Elecrow-RD/All-in-one-Starter-Kit-for-ESP32-P4-with-Common-Board-design/example/V1.1/Arduino_code/Lesson09_Display/esp_panel_drivers_conf.h

/*
 * SPDX-FileCopyrightText: 2023-2025 Espressif Systems (Shanghai) CO LTD
 *
 * SPDX-License-Identifier: Apache-2.0
 */
/**
 * @file  esp_panel_drivers_conf.h
 * @brief Configuration file for ESP Panel Drivers
 *
 * This file contains all the configurations needed for ESP Panel Drivers.
 * Users can modify these configurations according to their requirements.
 */

#pragma once

// *INDENT-OFF*

////////////////////////////////////////////////////////////////////////////////////////////////////////////////////////
////////////////////////////////////////////////// Bus Configurations //////////////////////////////////////////////////
////////////////////////////////////////////////////////////////////////////////////////////////////////////////////////
/**
 * @brief Bus driver availability
 *
 * Enable or disable bus drivers used in the factory class. Disable to reduce code size.
 * Set to `1` to enable, `0` to disable.
 */
#define ESP_PANEL_DRIVERS_BUS_USE_ALL                   (1)
#if !ESP_PANEL_DRIVERS_BUS_USE_ALL
    #define ESP_PANEL_DRIVERS_BUS_USE_SPI               (0)
    #define ESP_PANEL_DRIVERS_BUS_USE_QSPI              (0)
    #define ESP_PANEL_DRIVERS_BUS_USE_RGB               (0)
    #define ESP_PANEL_DRIVERS_BUS_USE_I2C               (0)
    #define ESP_PANEL_DRIVERS_BUS_USE_MIPI_DSI          (1)
#endif // ESP_PANEL_DRIVERS_BUS_USE_ALL

/**
 * @brief Controls compilation of unused bus drivers
 *
 * Enable or disable compilation of unused bus drivers.
 * When set to `0`, code for unused bus drivers will be excluded to speed up compilation. At this time,
 * users should ensure that the bus driver is not used.
 *
 * Example with SPI:
 * (CONF1 = ESP_PANEL_DRIVERS_BUS_USE_SPI, CONF2 = ESP_PANEL_DRIVERS_BUS_COMPILE_UNUSED_DRIVERS)
 *
 * | CONF1 | CONF2 | Driver Available ( = CONF1 ^ CONF2) | Factory Support ( = CONF1) |
 * |-------|-------|-------------------------------------|----------------------------|
 * |   0   |   0   |                 No                  |              No            |
 * |   1   |   0   |                 Yes                 |              Yes           |
 * |   0   |   1   |                 Yes                 |              No            |
 * |   1   |   1   |                 Yes                 |              Yes           |
 */
#define ESP_PANEL_DRIVERS_BUS_COMPILE_UNUSED_DRIVERS    (1)

////////////////////////////////////////////////////////////////////////////////////////////////////////////////////////
///////////////////////////////////////////////// LCD Configurations ///////////////////////////////////////////////////
////////////////////////////////////////////////////////////////////////////////////////////////////////////////////////
/**
 * @brief LCD driver availability
 *
 * Enable or disable LCD drivers used in the factory class. Disable to reduce code size.
 * Set to `1` to enable, `0` to disable.
 */
#define ESP_PANEL_DRIVERS_LCD_USE_ALL                   (0)
#if !ESP_PANEL_DRIVERS_LCD_USE_ALL
    #define ESP_PANEL_DRIVERS_LCD_USE_AXS15231B         (0)
    #define ESP_PANEL_DRIVERS_LCD_USE_EK9716B           (0)
    #define ESP_PANEL_DRIVERS_LCD_USE_EK79007           (1)
    #define ESP_PANEL_DRIVERS_LCD_USE_GC9A01            (0)
    #define ESP_PANEL_DRIVERS_LCD_USE_GC9B71            (0)
    #define ESP_PANEL_DRIVERS_LCD_USE_GC9503            (0)
    #define ESP_PANEL_DRIVERS_LCD_USE_HX8399            (0)
    #define ESP_PANEL_DRIVERS_LCD_USE_ILI9341           (0)
    #define ESP_PANEL_DRIVERS_LCD_USE_ILI9881C          (0)
    #define ESP_PANEL_DRIVERS_LCD_USE_JD9165            (0)
    #define ESP_PANEL_DRIVERS_LCD_USE_JD9365            (0)
    #define ESP_PANEL_DRIVERS_LCD_USE_NV3022B           (0)
    #define ESP_PANEL_DRIVERS_LCD_USE_SH8601            (0)
    #define ESP_PANEL_DRIVERS_LCD_USE_SPD2010           (0)
    #define ESP_PANEL_DRIVERS_LCD_USE_ST7262            (0)
    #define ESP_PANEL_DRIVERS_LCD_USE_ST7701            (0)
    #define ESP_PANEL_DRIVERS_LCD_USE_ST7703            (0)
    #define ESP_PANEL_DRIVERS_LCD_USE_ST7789            (0)
    #define ESP_PANEL_DRIVERS_LCD_USE_ST7796            (0)
    #define ESP_PANEL_DRIVERS_LCD_USE_ST77903           (0)
    #define ESP_PANEL_DRIVERS_LCD_USE_ST77916           (0)
    #define ESP_PANEL_DRIVERS_LCD_USE_ST77922           (0)
#endif // ESP_PANEL_DRIVERS_LCD_USE_ALL

/**
 * @brief Controls compilation of unused LCD drivers
 *
 * Enable or disable compilation of unused LCD drivers.
 * When set to `0`, code for unused LCD drivers will be excluded to speed up compilation. At this time,
 * users should ensure that the LCD driver is not used.
 *
 * Example with ILI9341:
 * (CONF1 = ESP_PANEL_DRIVERS_LCD_USE_ILI9341, CONF2 = ESP_PANEL_DRIVERS_LCD_COMPILE_UNUSED_DRIVERS)
 *
 * | CONF1 | CONF2 | Driver Available ( = CONF1 ^ CONF2) | Factory Support ( = CONF1) |
 * |-------|-------|-------------------------------------|----------------------------|
 * |   0   |   0   |                 No                  |              No            |
 * |   1   |   0   |                 Yes                 |              Yes           |
 * |   0   |   1   |                 Yes                 |              No            |
 * |   1   |   1   |                 Yes                 |              Yes           |
 */
#define ESP_PANEL_DRIVERS_LCD_COMPILE_UNUSED_DRIVERS    (1)

////////////////////////////////////////////////////////////////////////////////////////////////////////////////////////
///////////////////////////////////////////////// Touch Configurations /////////////////////////////////////////////////
////////////////////////////////////////////////////////////////////////////////////////////////////////////////////////
/**
 * @brief Touch panel configuration parameters
 */
#define ESP_PANEL_DRIVERS_TOUCH_MAX_POINTS              (10)    // Maximum number of touch points supported
#define ESP_PANEL_DRIVERS_TOUCH_MAX_BUTTONS             (5)     // Maximum number of touch buttons supported

/**
 * @brief Touch driver availability
 *
 * Enable or disable touch drivers used in the factory class. Disable to reduce code size.
 * Set to `1` to enable, `0` to disable.
 */
#define ESP_PANEL_DRIVERS_TOUCH_USE_ALL                 (0)
#if !ESP_PANEL_DRIVERS_TOUCH_USE_ALL
    #define ESP_PANEL_DRIVERS_TOUCH_USE_AXS15231B       (0)
    #define ESP_PANEL_DRIVERS_TOUCH_USE_CHSC6540        (0)
    #define ESP_PANEL_DRIVERS_TOUCH_USE_CST816S         (0)
    #define ESP_PANEL_DRIVERS_TOUCH_USE_CST820          (0)
    #define ESP_PANEL_DRIVERS_TOUCH_USE_FT5x06          (0)
    #define ESP_PANEL_DRIVERS_TOUCH_USE_GT911           (1)
    #define ESP_PANEL_DRIVERS_TOUCH_USE_GT1151          (0)
    #define ESP_PANEL_DRIVERS_TOUCH_USE_SPD2010         (0)
    #define ESP_PANEL_DRIVERS_TOUCH_USE_ST1633          (0)
    #define ESP_PANEL_DRIVERS_TOUCH_USE_ST7123          (0)
    #define ESP_PANEL_DRIVERS_TOUCH_USE_STMPE610        (0)
    #define ESP_PANEL_DRIVERS_TOUCH_USE_TT21100         (0)
    #define ESP_PANEL_DRIVERS_TOUCH_USE_XPT2046         (0)
#endif // ESP_PANEL_DRIVERS_TOUCH_USE_ALL

/**
 * @brief Controls compilation of unused touch drivers
 *
 * Enable or disable compilation of unused touch drivers.
 * When set to `0`, code for unused touch drivers will be excluded to speed up compilation. At this time,
 * users should ensure that the touch driver is not used.
 *
 * Example with GT911:
 * (CONF1 = ESP_PANEL_DRIVERS_TOUCH_USE_GT911, CONF2 = ESP_PANEL_DRIVERS_TOUCH_COMPILE_UNUSED_DRIVERS)
 *
 * | CONF1 | CONF2 | Driver Available ( = CONF1 ^ CONF2) | Factory Support ( = CONF1) |
 * |-------|-------|-------------------------------------|----------------------------|
 * |   0   |   0   |                 No                  |              No            |
 * |   1   |   0   |                 Yes                 |              Yes           |
 * |   0   |   1   |                 Yes                 |              No            |
 * |   1   |   1   |                 Yes                 |              Yes           |
 */
#define ESP_PANEL_DRIVERS_TOUCH_COMPILE_UNUSED_DRIVERS          (1)

#if ESP_PANEL_DRIVERS_TOUCH_USE_XPT2046 || ESP_PANEL_DRIVERS_TOUCH_COMPILE_UNUSED_DRIVERS
/**
 * @brief XPT2046 touch panel specific configurations
 */

#define ESP_PANEL_DRIVERS_TOUCH_XPT2046_Z_THRESHOLD             (400)  // Minimum pressure threshold for touch detection

/**
 * @brief Enable interrupt (PENIRQ) output mode
 *
 * When enabled, XPT2046 outputs low on PENIRQ when touch is detected (Full Power Mode).
 * Consumes more power but provides interrupt capability.
 */
#define ESP_PANEL_DRIVERS_TOUCH_XPT2046_INTERRUPT_MODE          (0)

/**
 * @brief Keep internal voltage reference enabled
 *
 * When enabled, internal Vref remains on between conversions. Slightly higher power consumption,
 * but requires fewer transactions for battery voltage, aux voltage and temperature readings.
 */
#define ESP_PANEL_DRIVERS_TOUCH_XPT2046_VREF_ON_MODE            (0)

/**
 * @brief Enable automatic coordinate conversion
 *
 * When enabled, raw ADC values (0-4096) are converted to screen coordinates.
 * When disabled, `process_coordinates` must be called manually to convert values.
 */
#define ESP_PANEL_DRIVERS_TOUCH_XPT2046_CONVERT_ADC_TO_COORDS   (1)

/**
 * @brief Enable data structure locking
 *
 * When enabled, driver locks touch position data structures during reads.
 * Warning: May cause unexpected crashes.
 */
#define ESP_PANEL_DRIVERS_TOUCH_XPT2046_ENABLE_LOCKING          (0)
#endif // ESP_PANEL_DRIVERS_TOUCH_USE_XPT2046 || ESP_PANEL_DRIVERS_TOUCH_COMPILE_UNUSED_DRIVERS

////////////////////////////////////////////////////////////////////////////////////////////////////////////////////////
////////////////////////////////////////////// IO Expander Configurations //////////////////////////////////////////////
////////////////////////////////////////////////////////////////////////////////////////////////////////////////////////
/**
 * @brief IO Expander driver availability
 *
 * Enable or disable IO Expander drivers used in the factory class. Disable to reduce code size.
 * Set to `1` to enable, `0` to disable.
 */
#define ESP_PANEL_DRIVERS_EXPANDER_USE_ALL                      (0)
#if !ESP_PANEL_DRIVERS_EXPANDER_USE_ALL
    #define ESP_PANEL_DRIVERS_EXPANDER_USE_CH422G               (0)
    #define ESP_PANEL_DRIVERS_EXPANDER_USE_HT8574               (0)
    #define ESP_PANEL_DRIVERS_EXPANDER_USE_TCA95XX_8BIT         (0)
    #define ESP_PANEL_DRIVERS_EXPANDER_USE_TCA95XX_16BIT        (0)
#endif // ESP_PANEL_DRIVERS_EXPANDER_USE_ALL

////////////////////////////////////////////////////////////////////////////////////////////////////////////////////////
/////////////////////////////////////////////// Backlight Configurations ///////////////////////////////////////////////
////////////////////////////////////////////////////////////////////////////////////////////////////////////////////////
/**
 * @brief Backlight driver availability
 *
 * Enable or disable backlight drivers used in the factory class. Disable to reduce code size.
 * Set to `1` to enable, `0` to disable.
 */
#define ESP_PANEL_DRIVERS_BACKLIGHT_USE_ALL                     (1)
#if !ESP_PANEL_DRIVERS_BACKLIGHT_USE_ALL
    #define ESP_PANEL_DRIVERS_BACKLIGHT_USE_SWITCH_GPIO         (0)
    #define ESP_PANEL_DRIVERS_BACKLIGHT_USE_SWITCH_EXPANDER     (0)
    #define ESP_PANEL_DRIVERS_BACKLIGHT_USE_PWM_LEDC            (0)
    #define ESP_PANEL_DRIVERS_BACKLIGHT_USE_CUSTOM              (0)
#endif // ESP_PANEL_DRIVERS_BACKLIGHT_USE_ALL

/**
 * @brief Controls compilation of unused backlight drivers
 *
 * Enable or disable compilation of unused backlight drivers.
 * When set to `0`, code for unused backlight drivers will be excluded to speed up compilation. At this time,
 * users should ensure that the backlight driver is not used.
 *
 * Example with PWM_LEDC:
 * (CONF1 = ESP_PANEL_DRIVERS_BACKLIGHT_USE_PWM_LEDC, CONF2 = ESP_PANEL_DRIVERS_BACKLIGHT_COMPILE_UNUSED_DRIVERS)
 *
 * | CONF1 | CONF2 | Driver Available ( = CONF1 ^ CONF2) | Factory Support ( = CONF1) |
 * |-------|-------|-------------------------------------|----------------------------|
 * |   0   |   0   |                 No                  |              No            |
 * |   1   |   0   |                 Yes                 |              Yes           |
 * |   0   |   1   |                 Yes                 |              No            |
 * |   1   |   1   |                 Yes                 |              Yes           |
 */
#define ESP_PANEL_DRIVERS_BACKLIGHT_COMPILE_UNUSED_DRIVERS     (1)

////////////////////////////////////////////////////////////////////////////////////////////////////////////////////////
/////////////////////////////////////////////// File Version ///////////////////////////////////////////////////////////
////////////////////////////////////////////////////////////////////////////////////////////////////////////////////////
/**
 * Do not change the following versions. These version numbers are used to check compatibility between this
 * configuration file and the library. Rules for version numbers:
 * 1. Major version mismatch: Configurations are incompatible, must use library version
 * 2. Minor version mismatch: May be missing new configurations, recommended to update
 * 3. Patch version mismatch: No impact on functionality
 */
#define ESP_PANEL_DRIVERS_CONF_FILE_VERSION_MAJOR 1
#define ESP_PANEL_DRIVERS_CONF_FILE_VERSION_MINOR 1
#define ESP_PANEL_DRIVERS_CONF_FILE_VERSION_PATCH 0

// *INDENT-ON*
