Elecrow-RD/All-in-one-Starter-Kit-for-ESP32-P4-with-Common-Board-design/factory_sourcecode/ESP32P4-dev-kits-ui/main/main.cpp

#include "freertos/FreeRTOS.h"
#include "freertos/task.h"
#include "nvs_flash.h"
#include "nvs.h"
#include "esp_log.h"
#include "esp_err.h"
#include "esp_check.h"
#include "esp_memory_utils.h"
#include "esp_heap_caps.h"
#include "esp_ldo_regulator.h"
#include "lvgl.h"
#include "bsp/esp-bsp.h"
#include "bsp/display.h"
#include "bsp_board_extra.h"

#include "esp_brookesia.hpp"
#include "app_examples/phone/squareline/src/phone_app_squareline.hpp"
#include "apps.h"

static const char *TAG = "main";

extern "C" void app_main(void)
{
    esp_err_t err = nvs_flash_init();
    if (err == ESP_ERR_NVS_NO_FREE_PAGES || err == ESP_ERR_NVS_NEW_VERSION_FOUND)
    {
        ESP_ERROR_CHECK(nvs_flash_erase());
        err = nvs_flash_init();
    }
    ESP_ERROR_CHECK(err);

    ESP_ERROR_CHECK(bsp_spiffs_mount());
    ESP_LOGI(TAG, "SPIFFS mount successfully");

#if CONFIG_EXAMPLE_ENABLE_SD_CARD
    ESP_ERROR_CHECK(bsp_sdcard_mount());
    ESP_LOGI(TAG, "SD card mount successfully");
#endif

    ESP_ERROR_CHECK(bsp_extra_codec_init());

    bsp_display_cfg_t cfg = {
        .lvgl_port_cfg = ESP_LVGL_PORT_INIT_CONFIG(),
        .buffer_size = BSP_LCD_H_RES * BSP_LCD_V_RES,
        .double_buffer = BSP_LCD_DRAW_BUFF_DOUBLE,
        .flags = {
            .buff_dma = false,
            .buff_spiram = true,
            .sw_rotate = false,
        }};
    bsp_display_start_with_config(&cfg);
    bsp_display_backlight_on();
    bsp_display_lock(0);
    elecrow_screen();
    bsp_display_unlock();
    while (!elecrow_success)
    {
        vTaskDelay(10 / portTICK_PERIOD_MS);
    }

    bsp_display_lock(0);
    ESP_Brookesia_Phone *phone = new ESP_Brookesia_Phone();
    assert(phone != nullptr && "Failed to create phone");

    ESP_Brookesia_PhoneStylesheet_t *phone_stylesheet = new ESP_Brookesia_PhoneStylesheet_t ESP_BROOKESIA_PHONE_1024_600_DARK_STYLESHEET();
    ESP_BROOKESIA_CHECK_NULL_EXIT(phone_stylesheet, "Create phone stylesheet failed");
    ESP_BROOKESIA_CHECK_FALSE_EXIT(phone->addStylesheet(*phone_stylesheet), "Add phone stylesheet failed");
    ESP_BROOKESIA_CHECK_FALSE_EXIT(phone->activateStylesheet(*phone_stylesheet), "Activate phone stylesheet failed");

    assert(phone->begin() && "Failed to begin phone");

    PhoneAppSquareline *smart_gadget = new PhoneAppSquareline();
    assert(smart_gadget != nullptr && "Failed to create phone app squareline");
    assert((phone->installApp(smart_gadget) >= 0) && "Failed to install phone app squareline");

    Calculator *calculator = new Calculator();
    assert(calculator != nullptr && "Failed to create calculator");
    assert((phone->installApp(calculator) >= 0) && "Failed to begin calculator");

    MusicPlayer *music_player = new MusicPlayer();
    assert(music_player != nullptr && "Failed to create music_player");
    assert((phone->installApp(music_player) >= 0) && "Failed to begin music_player");

    AppSettings *app_settings = new AppSettings();
    assert(app_settings != nullptr && "Failed to create app_settings");
    assert((phone->installApp(app_settings) >= 0) && "Failed to begin app_settings");

    Game2048 *game_2048 = new Game2048();
    assert(game_2048 != nullptr && "Failed to create game_2048");
    assert((phone->installApp(game_2048) >= 0) && "Failed to begin game_2048");

    // Camera *camera = new Camera(1280, 720);
    Camera *camera = new Camera(1024, 600);
    assert(camera != nullptr && "Failed to create camera");
    assert((phone->installApp(camera) >= 0) && "Failed to begin camera");

#if CONFIG_EXAMPLE_ENABLE_SD_CARD
    ESP_LOGW(TAG, "Using Video Player example requires inserting the SD card in advance and saving an MJPEG format video on the SD card");
    AppVideoPlayer *app_video_player = new AppVideoPlayer();
    assert(app_video_player != nullptr && "Failed to create app_video_player");
    assert((phone->installApp(app_video_player) >= 0) && "Failed to begin app_video_player");
#endif

    bsp_display_unlock();
}
