Elecrow-RD/All-in-one-Starter-Kit-for-ESP32-P4-with-Common-Board-design/factory_sourcecode/ESP32P4-dev-kits-ui/components/elecrow_esp32_p4_dev_kits/include/bsp/elecrow_esp32_p4_dev_kits.h

/*
 * SPDX-FileCopyrightText: 2024 Espressif Systems (Shanghai) CO LTD
 *
 * SPDX-License-Identifier: Apache-2.0
 */

/**
 * @file
 * @brief ESP BSP: ESP32-P4 Function EV Board
 */

#pragma once

#include "sdkconfig.h"
#include "driver/gpio.h"
#include "driver/i2c_master.h"
#include "driver/i2s_pdm.h"
#include "driver/sdmmc_host.h"
#include "driver/i2s_std.h"
#include "bsp/config.h"
#include "bsp/display.h"
#include "esp_codec_dev.h"
#include "sdkconfig.h"
#include "../../elecrow_ui/include/elecrow_ui.h"
#if (BSP_CONFIG_NO_GRAPHIC_LIB == 0)
#include "lvgl.h"
#include "esp_lvgl_port.h"
#endif // BSP_CONFIG_NO_GRAPHIC_LIB == 0

/**************************************************************************************************
 *  BSP Capabilities
 **************************************************************************************************/

#define BSP_CAPS_DISPLAY 1
#define BSP_CAPS_TOUCH 1
#define BSP_CAPS_BUTTONS 0
#define BSP_CAPS_AUDIO 1
#define BSP_CAPS_AUDIO_SPEAKER 1
#define BSP_CAPS_AUDIO_MIC 1
#define BSP_CAPS_SDCARD 1
#define BSP_CAPS_IMU 0

/**************************************************************************************************
 *  ESP-BOX pinout
 **************************************************************************************************/
/* I2C */
#define BSP_I2C_SCL (GPIO_NUM_19)
#define BSP_I2C_SDA (GPIO_NUM_18)

/* Audio */
#define BSP_I2S_MCLK (GPIO_NUM_NC)
#define BSP_I2S_SCLK (GPIO_NUM_22)
#define BSP_I2S_LCLK (GPIO_NUM_21)
#define BSP_I2S_DOUT (GPIO_NUM_23)
#define BSP_POWER_AMP_IO (GPIO_NUM_6)

#define BSP_I2S_CLK (GPIO_NUM_3)
#define BSP_I2S_DSIN (GPIO_NUM_4)

/* Display */
#if CONFIG_BSP_LCD_TYPE_1024_600
#define BSP_LCD_BACKLIGHT (GPIO_NUM_20)
#define BSP_LCD_RST (GPIO_NUM_5)
#define BSP_LCD_TOUCH_RST (GPIO_NUM_40)
#define BSP_LCD_TOUCH_INT (GPIO_NUM_41)
#define BSP_LCD_UPDN (GPIO_NUM_32)
#define BSP_LCD_SHLR (GPIO_NUM_33)
#else
#define BSP_LCD_BACKLIGHT (GPIO_NUM_23)
#define BSP_LCD_RST (GPIO_NUM_NC)
#define BSP_LCD_TOUCH_RST (GPIO_NUM_NC)
#define BSP_LCD_TOUCH_INT (GPIO_NUM_NC)
#endif

#ifdef __cplusplus
extern "C"
{
#endif

/**************************************************************************************************
 *
 * I2C interface
 *
 * There are multiple devices connected to I2C peripheral:
 *  - Codec ES8311 (configuration only)
 *  - LCD Touch controller
 **************************************************************************************************/
#define BSP_I2C_NUM CONFIG_BSP_I2C_NUM

    /**
     * @brief Init I2C driver
     *
     * @return
     *      - ESP_OK                On success
     *      - ESP_ERR_INVALID_ARG   I2C parameter error
     *      - ESP_FAIL              I2C driver installation error
     *
     */
    esp_err_t bsp_i2c_init(void);

    /**
     * @brief Deinit I2C driver and free its resources
     *
     * @return
     *      - ESP_OK                On success
     *      - ESP_ERR_INVALID_ARG   I2C parameter error
     *
     */
    esp_err_t bsp_i2c_deinit(void);

    /**
     * @brief Get I2C driver handle
     *
     * @return
     *      - I2C handle
     *
     */
    i2c_master_bus_handle_t bsp_i2c_get_handle(void);

    /**************************************************************************************************
     *
     * I2S audio interface
     *
     * There are two devices connected to the I2S peripheral:
     *  - Codec ES8311 for output(playback) and input(recording) path
     *
     * For speaker initialization use bsp_audio_codec_speaker_init() which is inside initialize I2S with bsp_audio_init().
     * For microphone initialization use bsp_audio_codec_microphone_init() which is inside initialize I2S with bsp_audio_init().
     * After speaker or microphone initialization, use functions from esp_codec_dev for play/record audio.
     * Example audio play:
     * \code{.c}
     * esp_codec_dev_set_out_vol(spk_codec_dev, DEFAULT_VOLUME);
     * esp_codec_dev_open(spk_codec_dev, &fs);
     * esp_codec_dev_write(spk_codec_dev, wav_bytes, bytes_read_from_spiffs);
     * esp_codec_dev_close(spk_codec_dev);
     * \endcode
     **************************************************************************************************/

    /**
     * @brief Init audio
     *
     * @note There is no deinit audio function. Users can free audio resources by calling i2s_del_channel()
     * @warning The type of i2s_config param is depending on IDF version.
     * @param[in]  i2s_config I2S configuration. Pass NULL to use default values (Mono, duplex, 16bit, 22050 Hz)
     * @return
     *      - ESP_OK                On success
     *      - ESP_ERR_NOT_SUPPORTED The communication mode is not supported on the current chip
     *      - ESP_ERR_INVALID_ARG   NULL pointer or invalid configuration
     *      - ESP_ERR_NOT_FOUND     No available I2S channel found
     *      - ESP_ERR_NO_MEM        No memory for storing the channel information
     *      - ESP_ERR_INVALID_STATE This channel has not initialized or already started
     */
    esp_err_t bsp_audio_init(const i2s_std_config_t *i2s_config);

    /**
     * @brief Initialize speaker codec device
     *
     * @return Pointer to codec device handle or NULL when error occurred
     */
    esp_codec_dev_handle_t bsp_audio_codec_speaker_init(void);

    /**
     * @brief Initialize microphone codec device
     *
     * @return Pointer to codec device handle or NULL when error occurred
     */
    esp_codec_dev_handle_t bsp_audio_codec_microphone_init(void);

/**************************************************************************************************
 *
 * SPIFFS
 *
 * After mounting the SPIFFS, it can be accessed with stdio functions ie.:
 * \code{.c}
 * FILE* f = fopen(BSP_SPIFFS_MOUNT_POINT"/hello.txt", "w");
 * fprintf(f, "Hello World!\n");
 * fclose(f);
 * \endcode
 **************************************************************************************************/
#define BSP_SPIFFS_MOUNT_POINT CONFIG_BSP_SPIFFS_MOUNT_POINT

    /**
     * @brief Mount SPIFFS to virtual file system
     *
     * @return
     *      - ESP_OK on success
     *      - ESP_ERR_INVALID_STATE if esp_vfs_spiffs_register was already called
     *      - ESP_ERR_NO_MEM if memory can not be allocated
     *      - ESP_FAIL if partition can not be mounted
     *      - other error codes
     */
    esp_err_t bsp_spiffs_mount(void);

    /**
     * @brief Unmount SPIFFS from virtual file system
     *
     * @return
     *      - ESP_OK on success
     *      - ESP_ERR_NOT_FOUND if the partition table does not contain SPIFFS partition with given label
     *      - ESP_ERR_INVALID_STATE if esp_vfs_spiffs_unregister was already called
     *      - ESP_ERR_NO_MEM if memory can not be allocated
     *      - ESP_FAIL if partition can not be mounted
     *      - other error codes
     */
    esp_err_t bsp_spiffs_unmount(void);

/**************************************************************************************************
 *
 * uSD card
 *
 * After mounting the uSD card, it can be accessed with stdio functions ie.:
 * \code{.c}
 * FILE* f = fopen(BSP_MOUNT_POINT"/hello.txt", "w");
 * fprintf(f, "Hello %s!\n", bsp_sdcard->cid.name);
 * fclose(f);
 * \endcode
 **************************************************************************************************/
#define BSP_SD_MOUNT_POINT CONFIG_BSP_SD_MOUNT_POINT
    extern sdmmc_card_t *bsp_sdcard;

    /**
     * @brief Mount microSD card to virtual file system
     *
     * @return
     *      - ESP_OK on success
     *      - ESP_ERR_INVALID_STATE if esp_vfs_fat_sdmmc_mount was already called
     *      - ESP_ERR_NO_MEM if memory cannot be allocated
     *      - ESP_FAIL if partition cannot be mounted
     *      - other error codes from SDMMC or SPI drivers, SDMMC protocol, or FATFS drivers
     */
    esp_err_t bsp_sdcard_mount(void);

    /**
     * @brief Unmount microSD card from virtual file system
     *
     * @return
     *      - ESP_OK on success
     *      - ESP_ERR_NOT_FOUND if the partition table does not contain FATFS partition with given label
     *      - ESP_ERR_INVALID_STATE if esp_vfs_fat_spiflash_mount was already called
     *      - ESP_ERR_NO_MEM if memory can not be allocated
     *      - ESP_FAIL if partition can not be mounted
     *      - other error codes from wear levelling library, SPI flash driver, or FATFS drivers
     */
    esp_err_t bsp_sdcard_unmount(void);

/**************************************************************************************************
 *
 * LCD interface
 *
 * ESP-BOX is shipped with 2.4inch ST7789 display controller.
 * It features 16-bit colors, 320x240 resolution and capacitive touch controller.
 *
 * LVGL is used as graphics library. LVGL is NOT thread safe, therefore the user must take LVGL mutex
 * by calling bsp_display_lock() before calling and LVGL API (lv_...) and then give the mutex with
 * bsp_display_unlock().
 *
 * Display's backlight must be enabled explicitly by calling bsp_display_backlight_on()
 **************************************************************************************************/
#define BSP_LCD_PIXEL_CLOCK_MHZ (80)

#if (BSP_CONFIG_NO_GRAPHIC_LIB == 0)

#define BSP_LCD_DRAW_BUFF_SIZE (BSP_LCD_H_RES * 50) // Frame buffer size in pixels
#define BSP_LCD_DRAW_BUFF_DOUBLE (0)

    /**
     * @brief BSP display configuration structure
     *
     */
    typedef struct
    {
        lvgl_port_cfg_t lvgl_port_cfg; /*!< LVGL port configuration */
        uint32_t buffer_size;          /*!< Size of the buffer for the screen in pixels */
        bool double_buffer;            /*!< True, if should be allocated two buffers */
        struct
        {
            unsigned int buff_dma : 1;    /*!< Allocated LVGL buffer will be DMA capable */
            unsigned int buff_spiram : 1; /*!< Allocated LVGL buffer will be in PSRAM */
            unsigned int sw_rotate : 1;   /*!< Use software rotation (slower), The feature is unavailable under avoid-tear mode */
        } flags;
    } bsp_display_cfg_t;

    /**
     * @brief Initialize display
     *
     * This function initializes SPI, display controller and starts LVGL handling task.
     * LCD backlight must be enabled separately by calling bsp_display_brightness_set()
     *
     * @return Pointer to LVGL display or NULL when error occured
     */
    lv_display_t *bsp_display_start(void);

    /**
     * @brief Initialize display
     *
     * This function initializes SPI, display controller and starts LVGL handling task.
     * LCD backlight must be enabled separately by calling bsp_display_brightness_set()
     *
     * @param cfg display configuration
     *
     * @return Pointer to LVGL display or NULL when error occured
     */
    lv_display_t *bsp_display_start_with_config(const bsp_display_cfg_t *cfg);

    /**
     * @brief Get pointer to input device (touch, buttons, ...)
     *
     * @note The LVGL input device is initialized in bsp_display_start() function.
     *
     * @return Pointer to LVGL input device or NULL when not initialized
     */
    lv_indev_t *bsp_display_get_input_dev(void);

    /**
     * @brief Take LVGL mutex
     *
     * @param timeout_ms Timeout in [ms]. 0 will block indefinitely.
     * @return true  Mutex was taken
     * @return false Mutex was NOT taken
     */
    bool bsp_display_lock(uint32_t timeout_ms);

    /**
     * @brief Give LVGL mutex
     *
     */
    void bsp_display_unlock(void);

    /**
     * @brief Rotate screen
     *
     * Display must be already initialized by calling bsp_display_start()
     *
     * @param[in] disp Pointer to LVGL display
     * @param[in] rotation Angle of the display rotation
     */
    void bsp_display_rotate(lv_display_t *disp, lv_disp_rotation_t rotation);
#endif // BSP_CONFIG_NO_GRAPHIC_LIB == 0

    /**************************************************************************************************
     *
     * USB
     *
     **************************************************************************************************/

    /**
     * @brief Power modes of USB Host connector
     */
    typedef enum bsp_usb_host_power_mode_t
    {
        BSP_USB_HOST_POWER_MODE_USB_DEV, //!< Power from USB DEV port
    } bsp_usb_host_power_mode_t;

    /**
     * @brief Start USB host
     *
     * This is a one-stop-shop function that will configure the board for USB Host mode
     * and start USB Host library
     *
     * @param[in] mode        USB Host connector power mode (Not used on this board)
     * @param[in] limit_500mA Limit output current to 500mA (Not used on this board)
     * @return
     *     - ESP_OK                 On success
     *     - ESP_ERR_INVALID_ARG    Parameter error
     *     - ESP_ERR_NO_MEM         Memory cannot be allocated
     */
    esp_err_t bsp_usb_host_start(bsp_usb_host_power_mode_t mode, bool limit_500mA);

    /**
     * @brief Stop USB host
     *
     * USB Host lib will be uninstalled and power from connector removed.
     *
     * @return
     *     - ESP_OK              On success
     *     - ESP_ERR_INVALID_ARG Parameter error
     */
    esp_err_t bsp_usb_host_stop(void);

#ifdef __cplusplus
}
#endif
