Elecrow-RD/All-in-one-Starter-Kit-for-ESP32-P4-with-Common-Board-design/example/V1.1/Arduino_code/Lesson12_Temp_Humi_sensor/bsp_dht20.h

#ifndef _BSP_DHT20_H_
#define _BSP_DHT20_H_

/*————————————————————————————————————————Header file declaration————————————————————————————————————————*/
#include <string.h>            //References for string Function-related API Functions
#include "freertos/FreeRTOS.h" //References for Freertos Function-related API Functions
#include "freertos/task.h"     //References for Freertos Task Function-related API Functions
#include "esp_log.h"           //References for LOG Printing Function-related API Functions
#include "esp_err.h"           //References for Error Type Function-related API Functions
#include "esp_timer.h"         //References for high-precision timers Function-related API Functions
#include "bsp_i2c.h"
/*——————————————————————————————————————Header file declaration end——————————————————————————————————————*/

/*——————————————————————————————————————————Variable declaration—————————————————————————————————————————*/
#define DHT20_TAG "DHT20"
#define DHT20_INFO(fmt, ...) ESP_LOGI(DHT20_TAG, fmt, ##__VA_ARGS__)
#define DHT20_DEBUG(fmt, ...) ESP_LOGD(DHT20_TAG, fmt, ##__VA_ARGS__)
#define DHT20_ERROR(fmt, ...) ESP_LOGE(DHT20_TAG, fmt, ##__VA_ARGS__)



#define DHT20_I2C_ADDRESS 0x38 // The 7-bit I2C address of DHT20

#define DHT20_MEASURE_TIMEOUT 1000 // Measurement timeout time of DHT20
typedef struct dht20_data
{
    float temperature;  // The measured temperature data
    float humidity;     // the measured humidity data
    uint32_t raw_humid; // Intermediate quantity for humidity data conversion
    uint32_t raw_temp;  // Intermediate quantity for temperature data conversion
} dht20_data_t;

esp_err_t dht20_begin(void);                   // Initialization of DHT20 sensor
esp_err_t dht20_is_calibrated(void);           // The function for determining whether the DHT20 sensor is ready or not
esp_err_t dht20_read_data(dht20_data_t *data); // DHT20 Sensor Temperature and Humidity Data Reading Function

/*———————————————————————————————————————Variable declaration end——————————————-—————————————————————————*/
#endif
